12zcab/SusGadget-Board/Images/3DB-removebg-preview.png

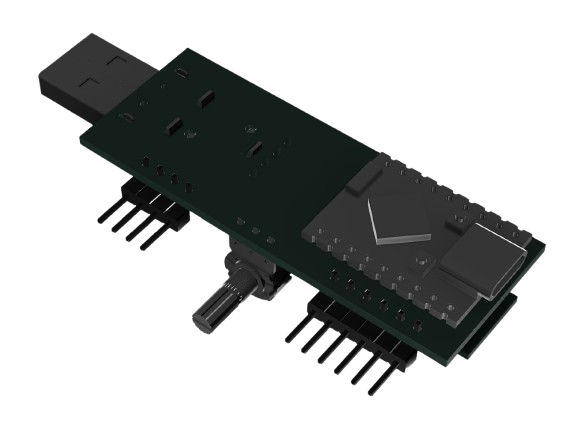
Images/3DB-removebg-preview.png
