12zcab/SusGadget-Board/Images/3DF-removebg-preview.png

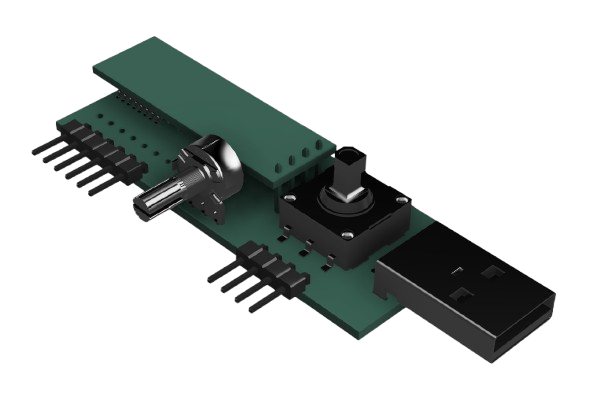
Images/3DF-removebg-preview.png
