12zcab/SusGadget-Board/Images/pcbb.png

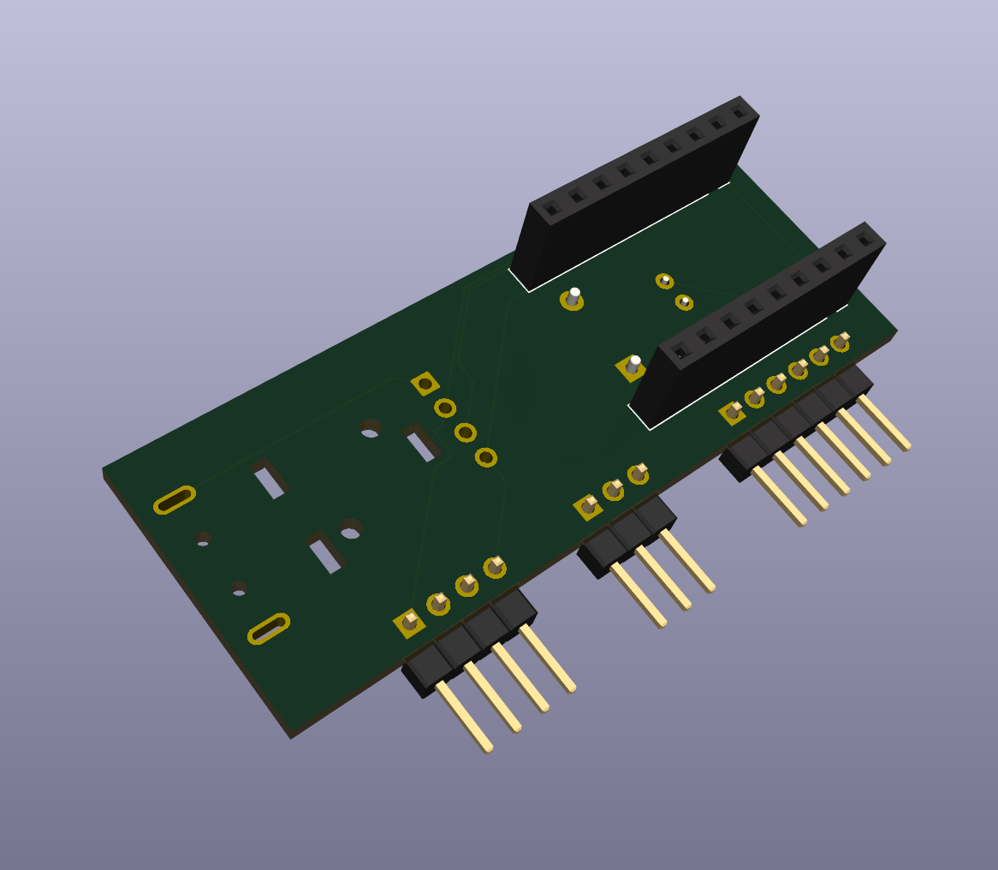
Images/pcbb.png
