12zcab/SusGadget-Board/Images/pcbf.png

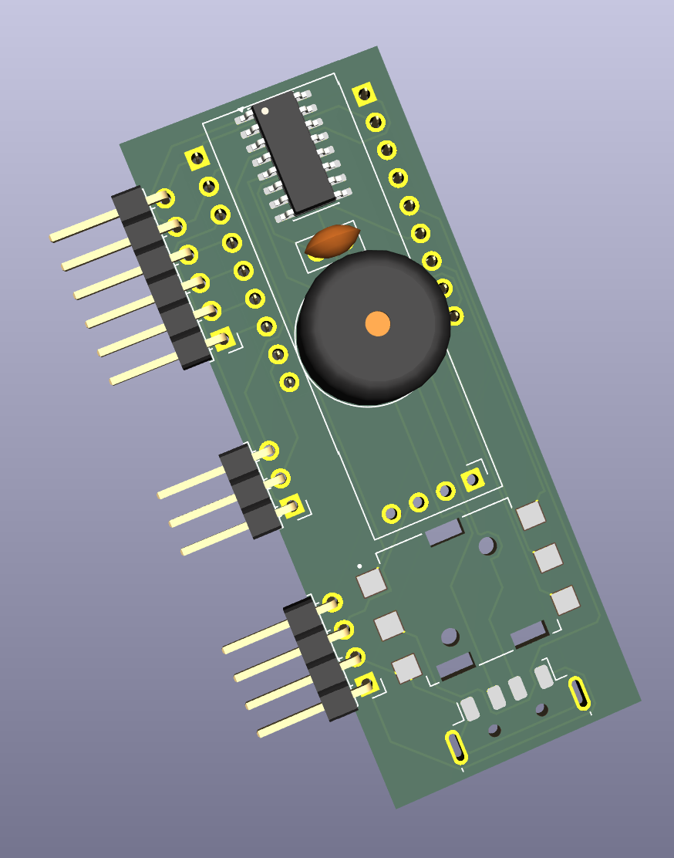
Images/pcbf.png
