12zcab/SusGadget-Board/Images/Screenshot 2026-08-23 151615.png

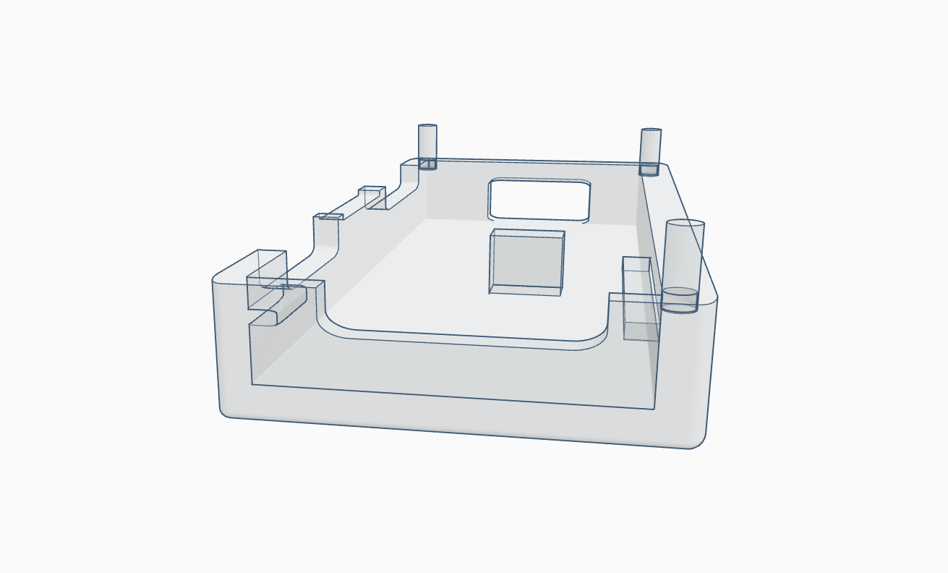
Images/Screenshot 2026-08-23 151615.png
