12zcab/SusGadget-Board/Images/Screenshot 2026-08-23 152606.png

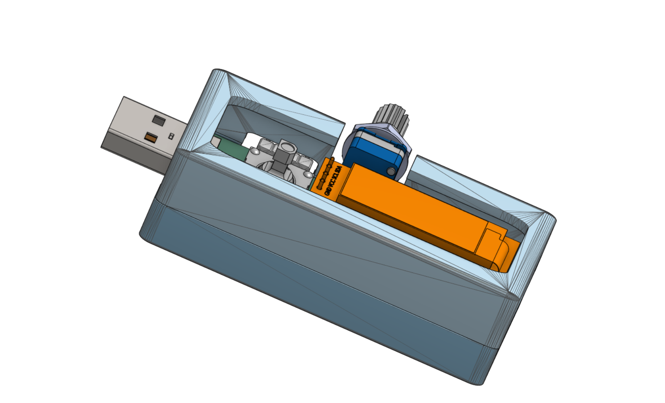
Images/Screenshot 2026-08-23 152606.png
