12zcab/SusGadget-Board/Zine/Zine.png

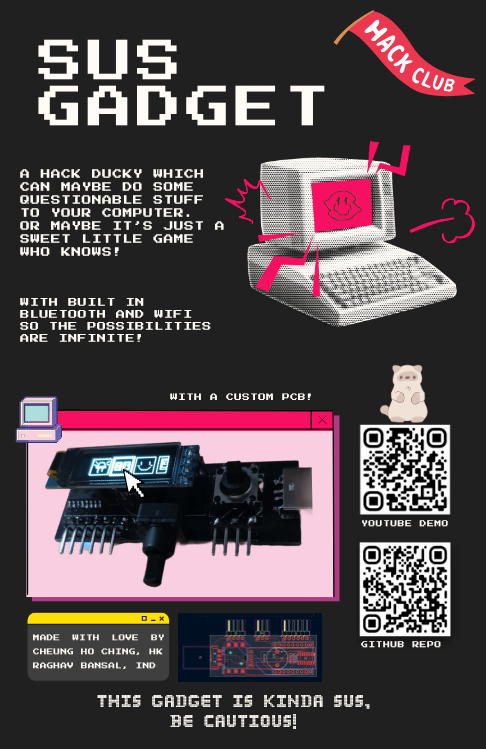
Zine/Zine.png
